NeedsMoreMayo/LC/LTSpice/Oscillator_LT1720_1uF.asc

C1: Cap; 1nF
C2: cap; 1µ
C4: Cap; 1µ
L1: ind; 82µ
R2: Res; 120K
R3: Res; 100K
R4: Res; 68K
R6: Res; 120K
U1: LT1720
V1: voltage; 5
Named nets: 0
.tran 2000m startup
